hollyspell/neo-watch-terminal/sentry_1bit.png

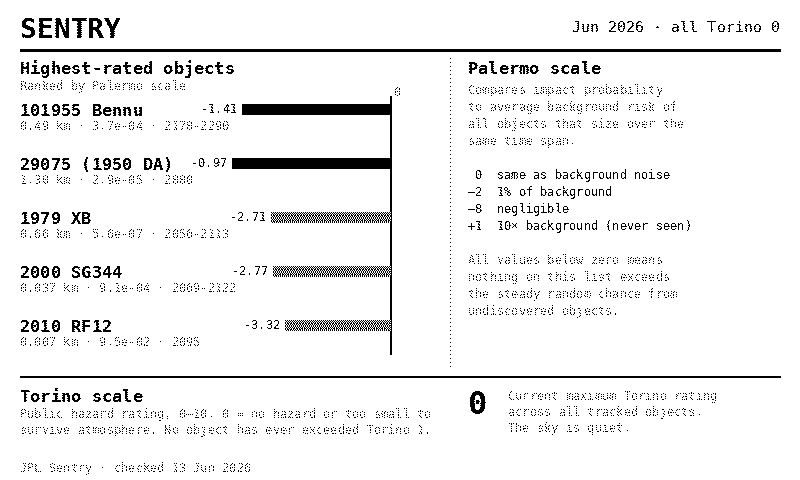
sentry_1bit.png
